anthonyjclarke/Solar-Lights-Lite/docs/drawings/breadboard-layout.png

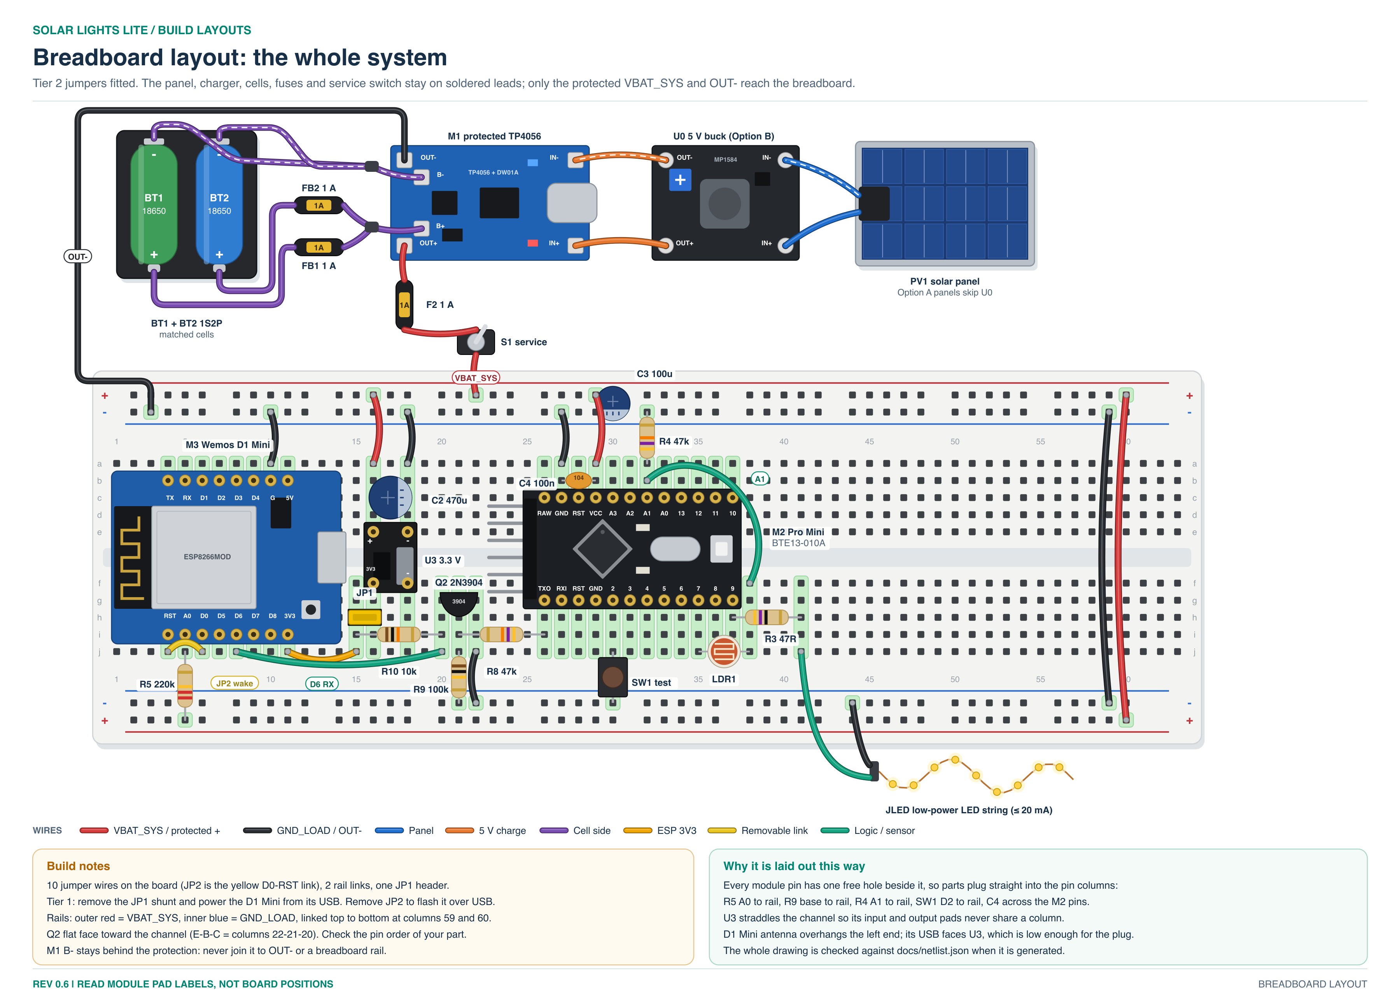
docs/drawings/breadboard-layout.png
