anthonyjclarke/Solar-Lights-Lite/docs/drawings/BTE13-010A-pin-map.png

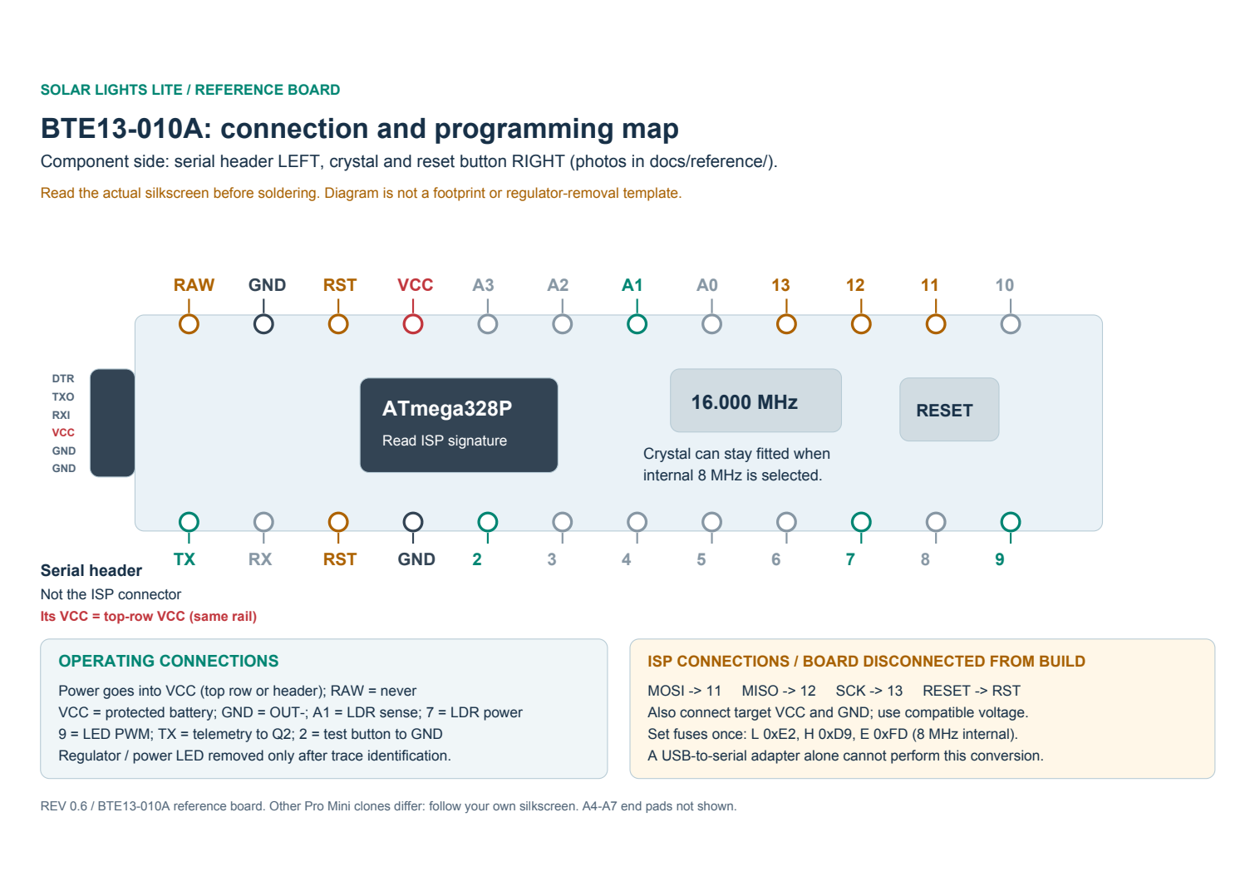
docs/drawings/BTE13-010A-pin-map.png
