anthonyjclarke/Solar-Lights-Lite/docs/drawings/controller-bench-sheet.png

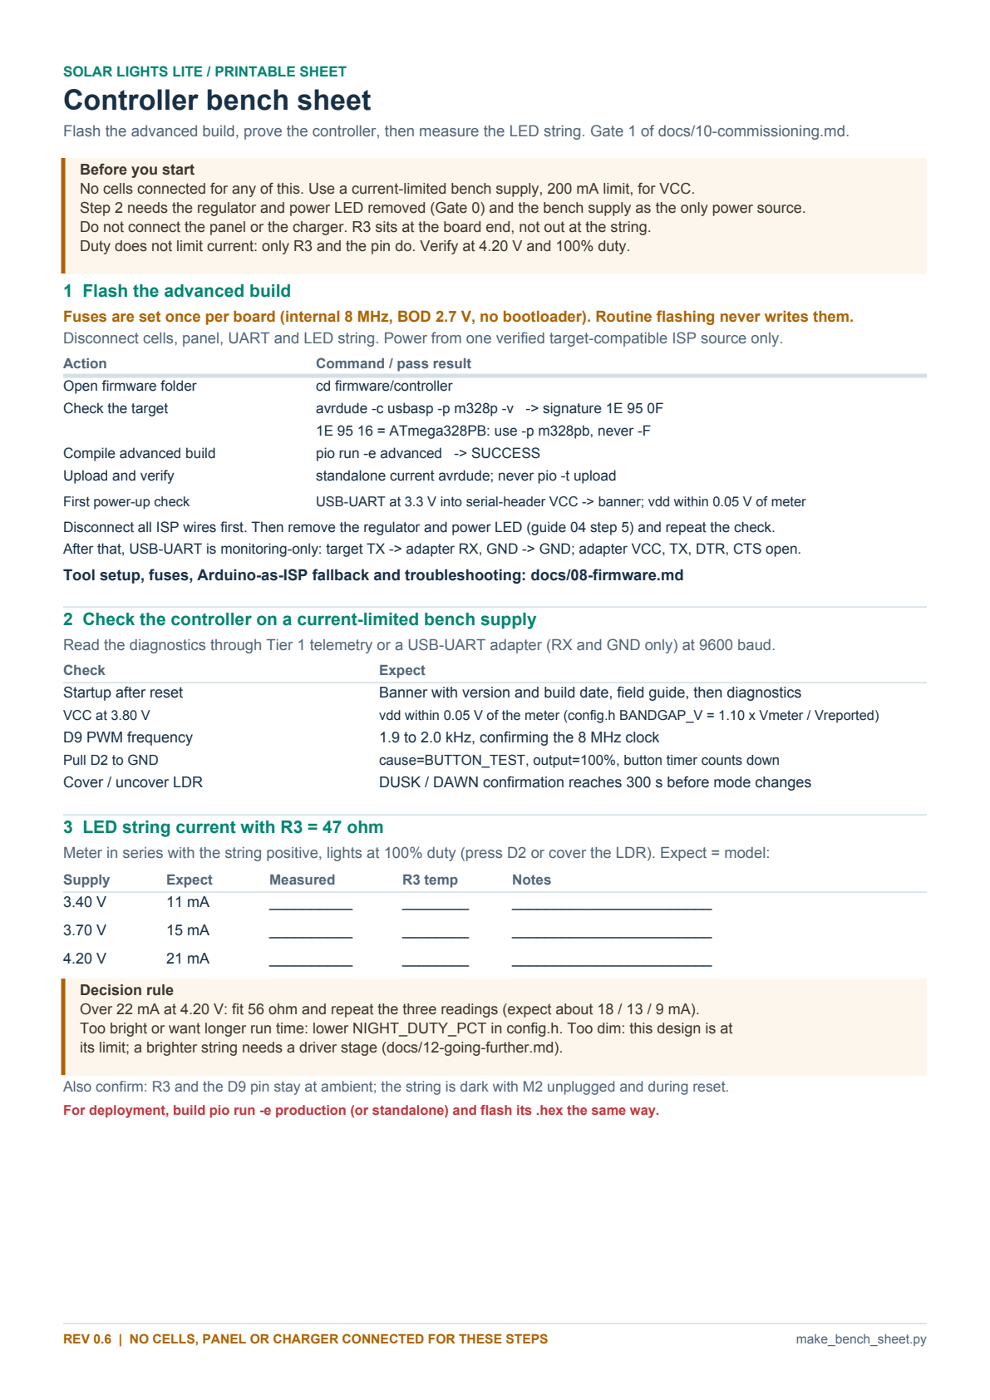
docs/drawings/controller-bench-sheet.png
