anthonyjclarke/Solar-Lights-Lite/docs/drawings/perfboard-layout.png

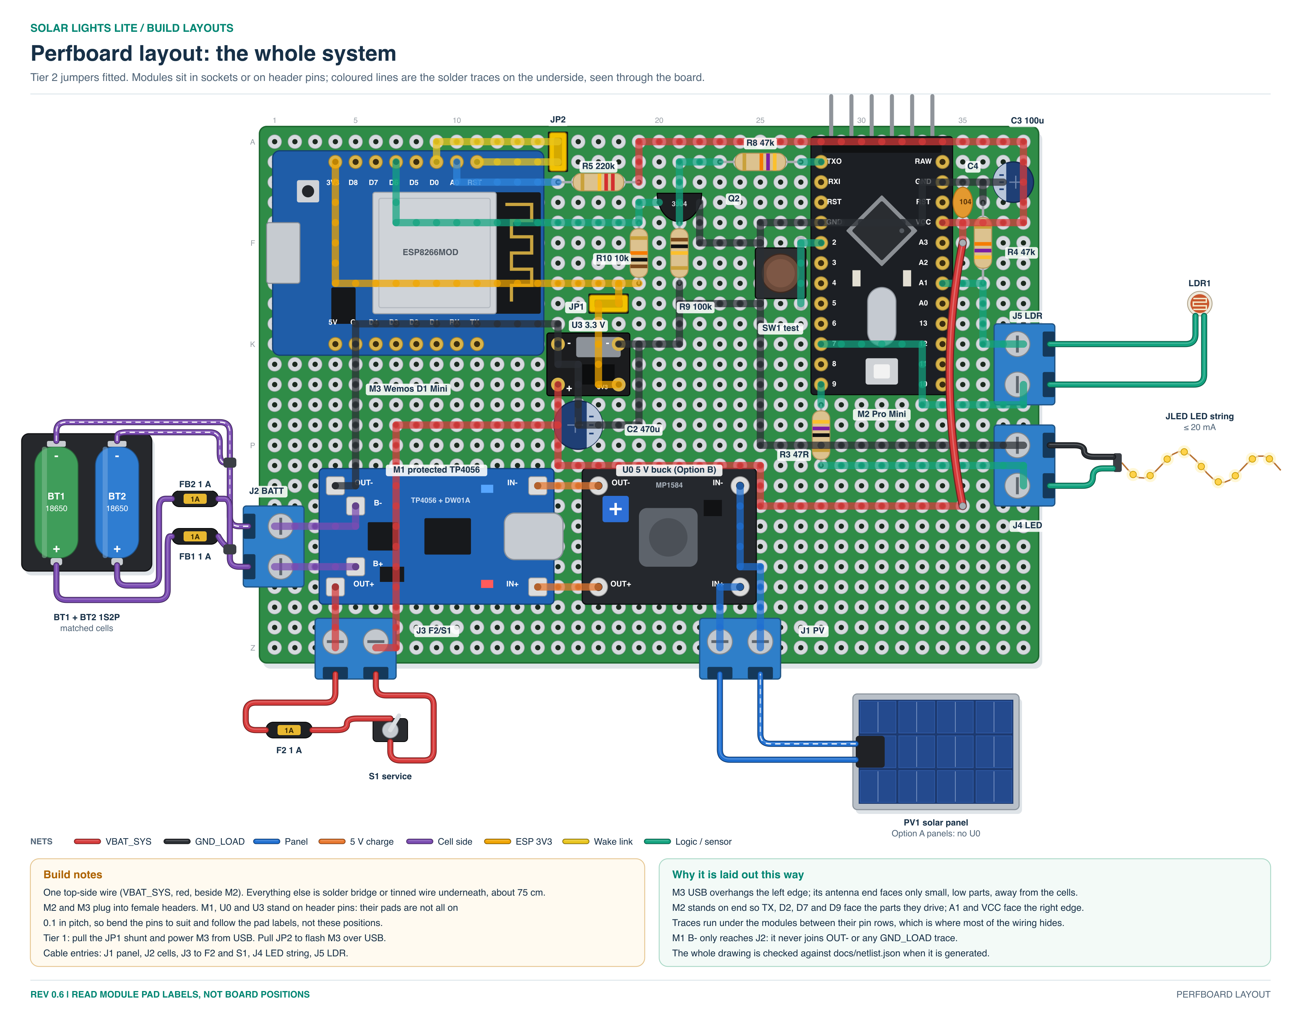
docs/drawings/perfboard-layout.png
