anthonyjclarke/Solar-Lights-Lite/docs/drawings/sheet-1.png

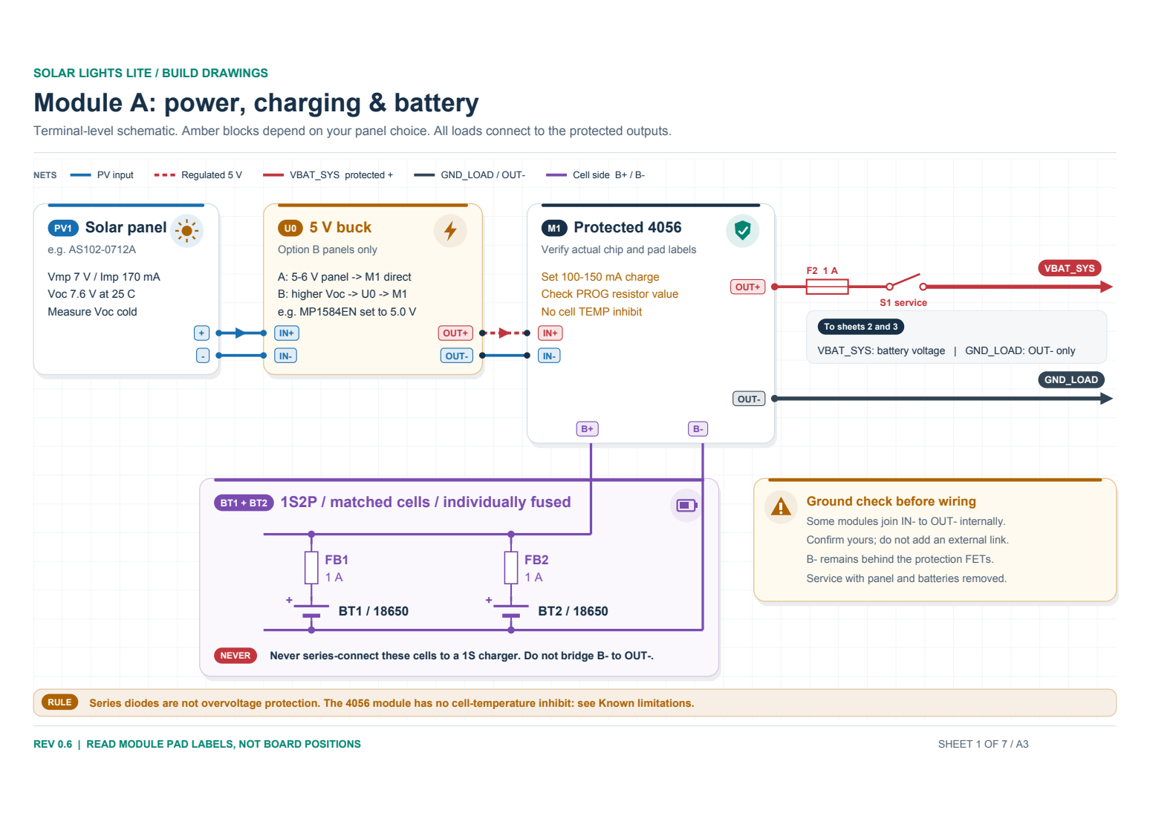
docs/drawings/sheet-1.png
