anthonyjclarke/Solar-Lights-Lite/docs/drawings/sheet-2.png

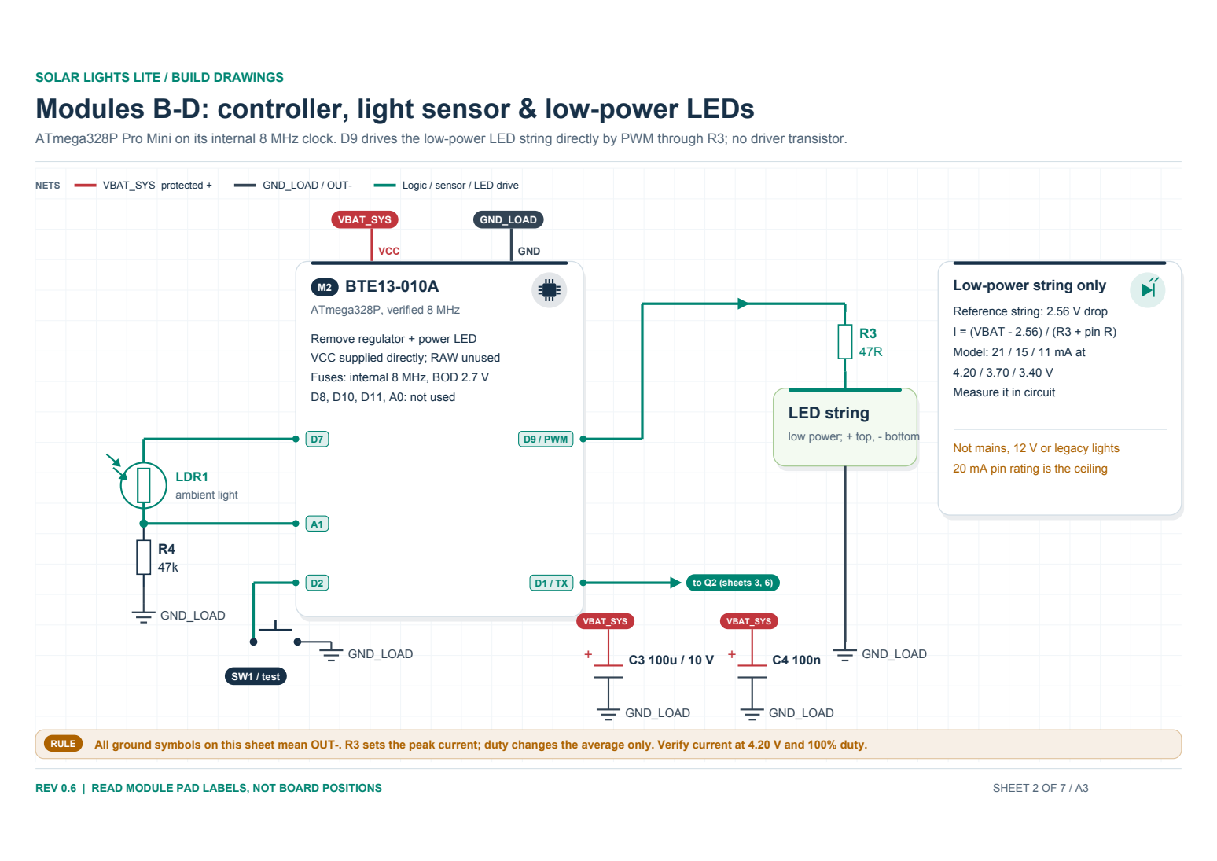
docs/drawings/sheet-2.png
