anthonyjclarke/Solar-Lights-Lite/docs/drawings/sheet-4.png

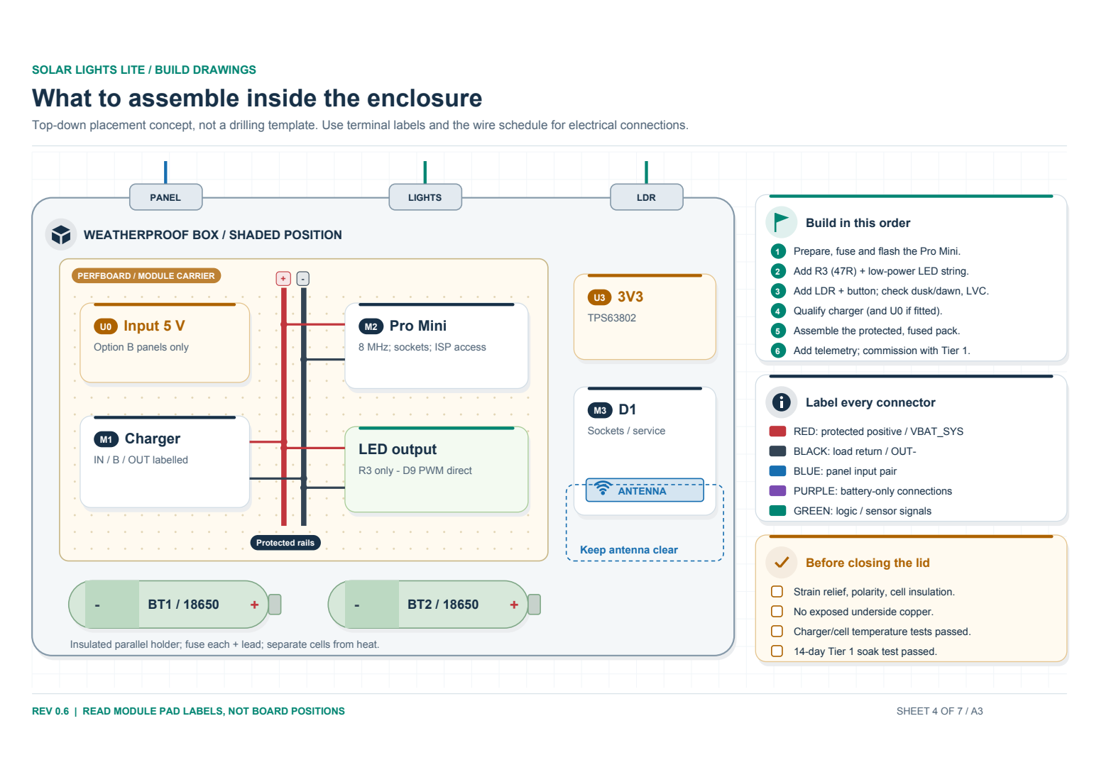
docs/drawings/sheet-4.png
