anthonyjclarke/Solar-Lights-Lite/docs/reference/BTE13-010A-front.jpeg

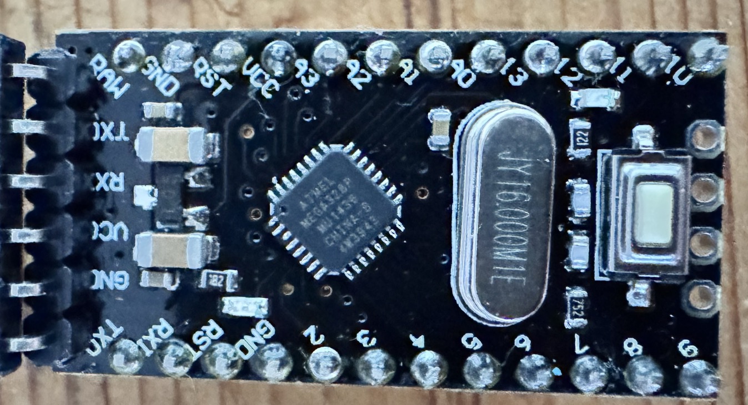
docs/reference/BTE13-010A-front.jpeg
