anthonyjclarke/Solar-Lights-Lite/docs/reference/charger-module-4056.jpg

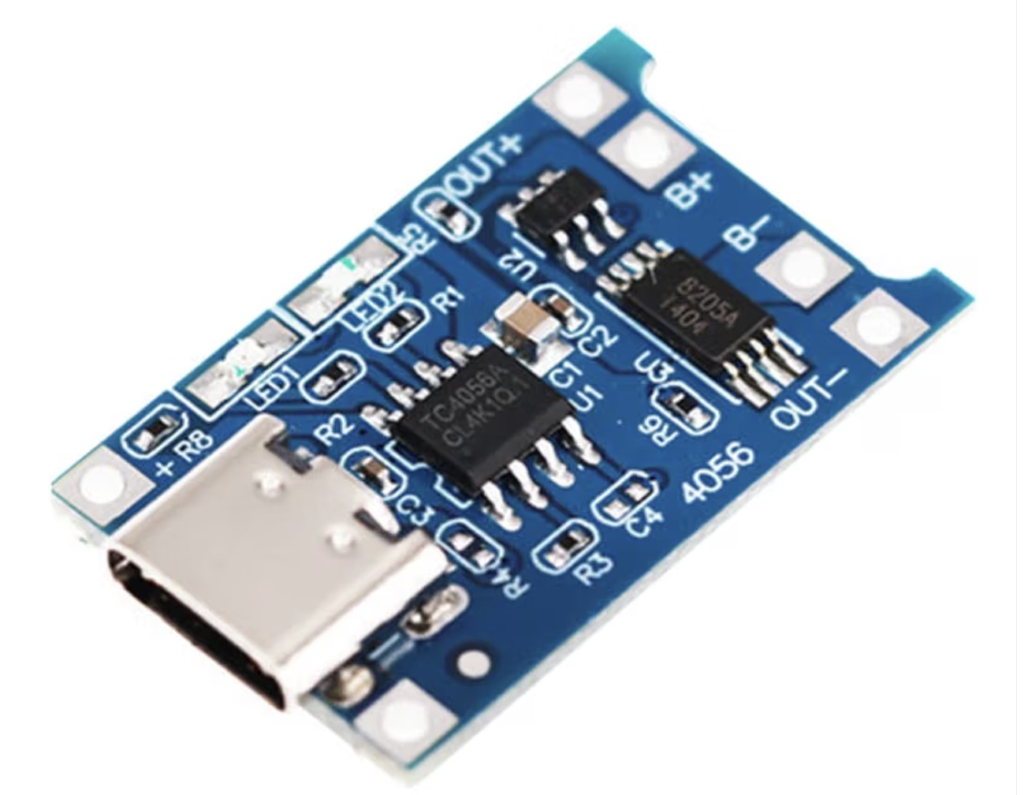
docs/reference/charger-module-4056.jpg
