anthonyjclarke/Solar-Lights-Lite/docs/reference/ProMini-328PB-front.jpeg

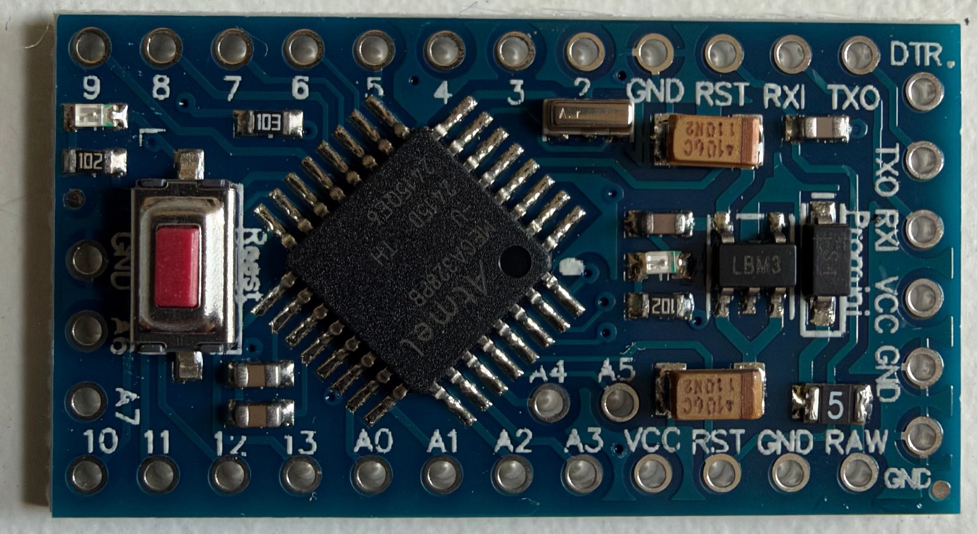
docs/reference/ProMini-328PB-front.jpeg
