anthonyjclarke/Solar-Lights-Lite/docs/reference/solar-panel-AS102-0712A.jpg

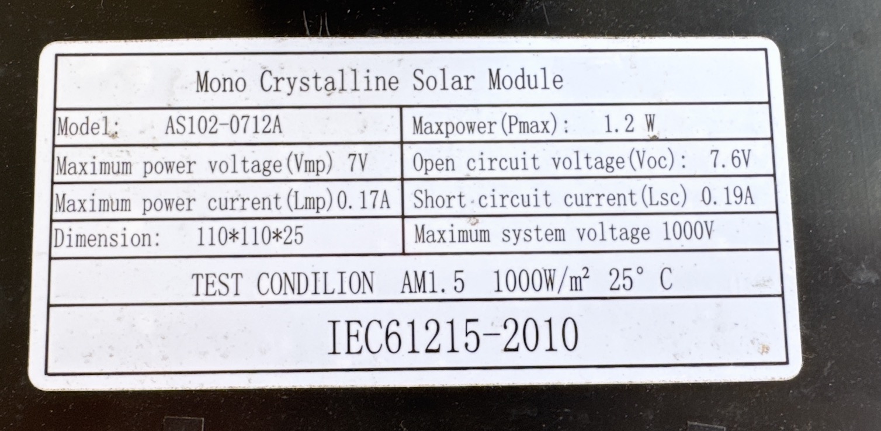
docs/reference/solar-panel-AS102-0712A.jpg
