anthonyjclarke/Solar-Lights-Lite/hardware/kicad/SolarLights_Lite.kicad_sch

## KiCad design hardware/kicad/SolarLights_Lite.kicad_sch (2026-09-30)

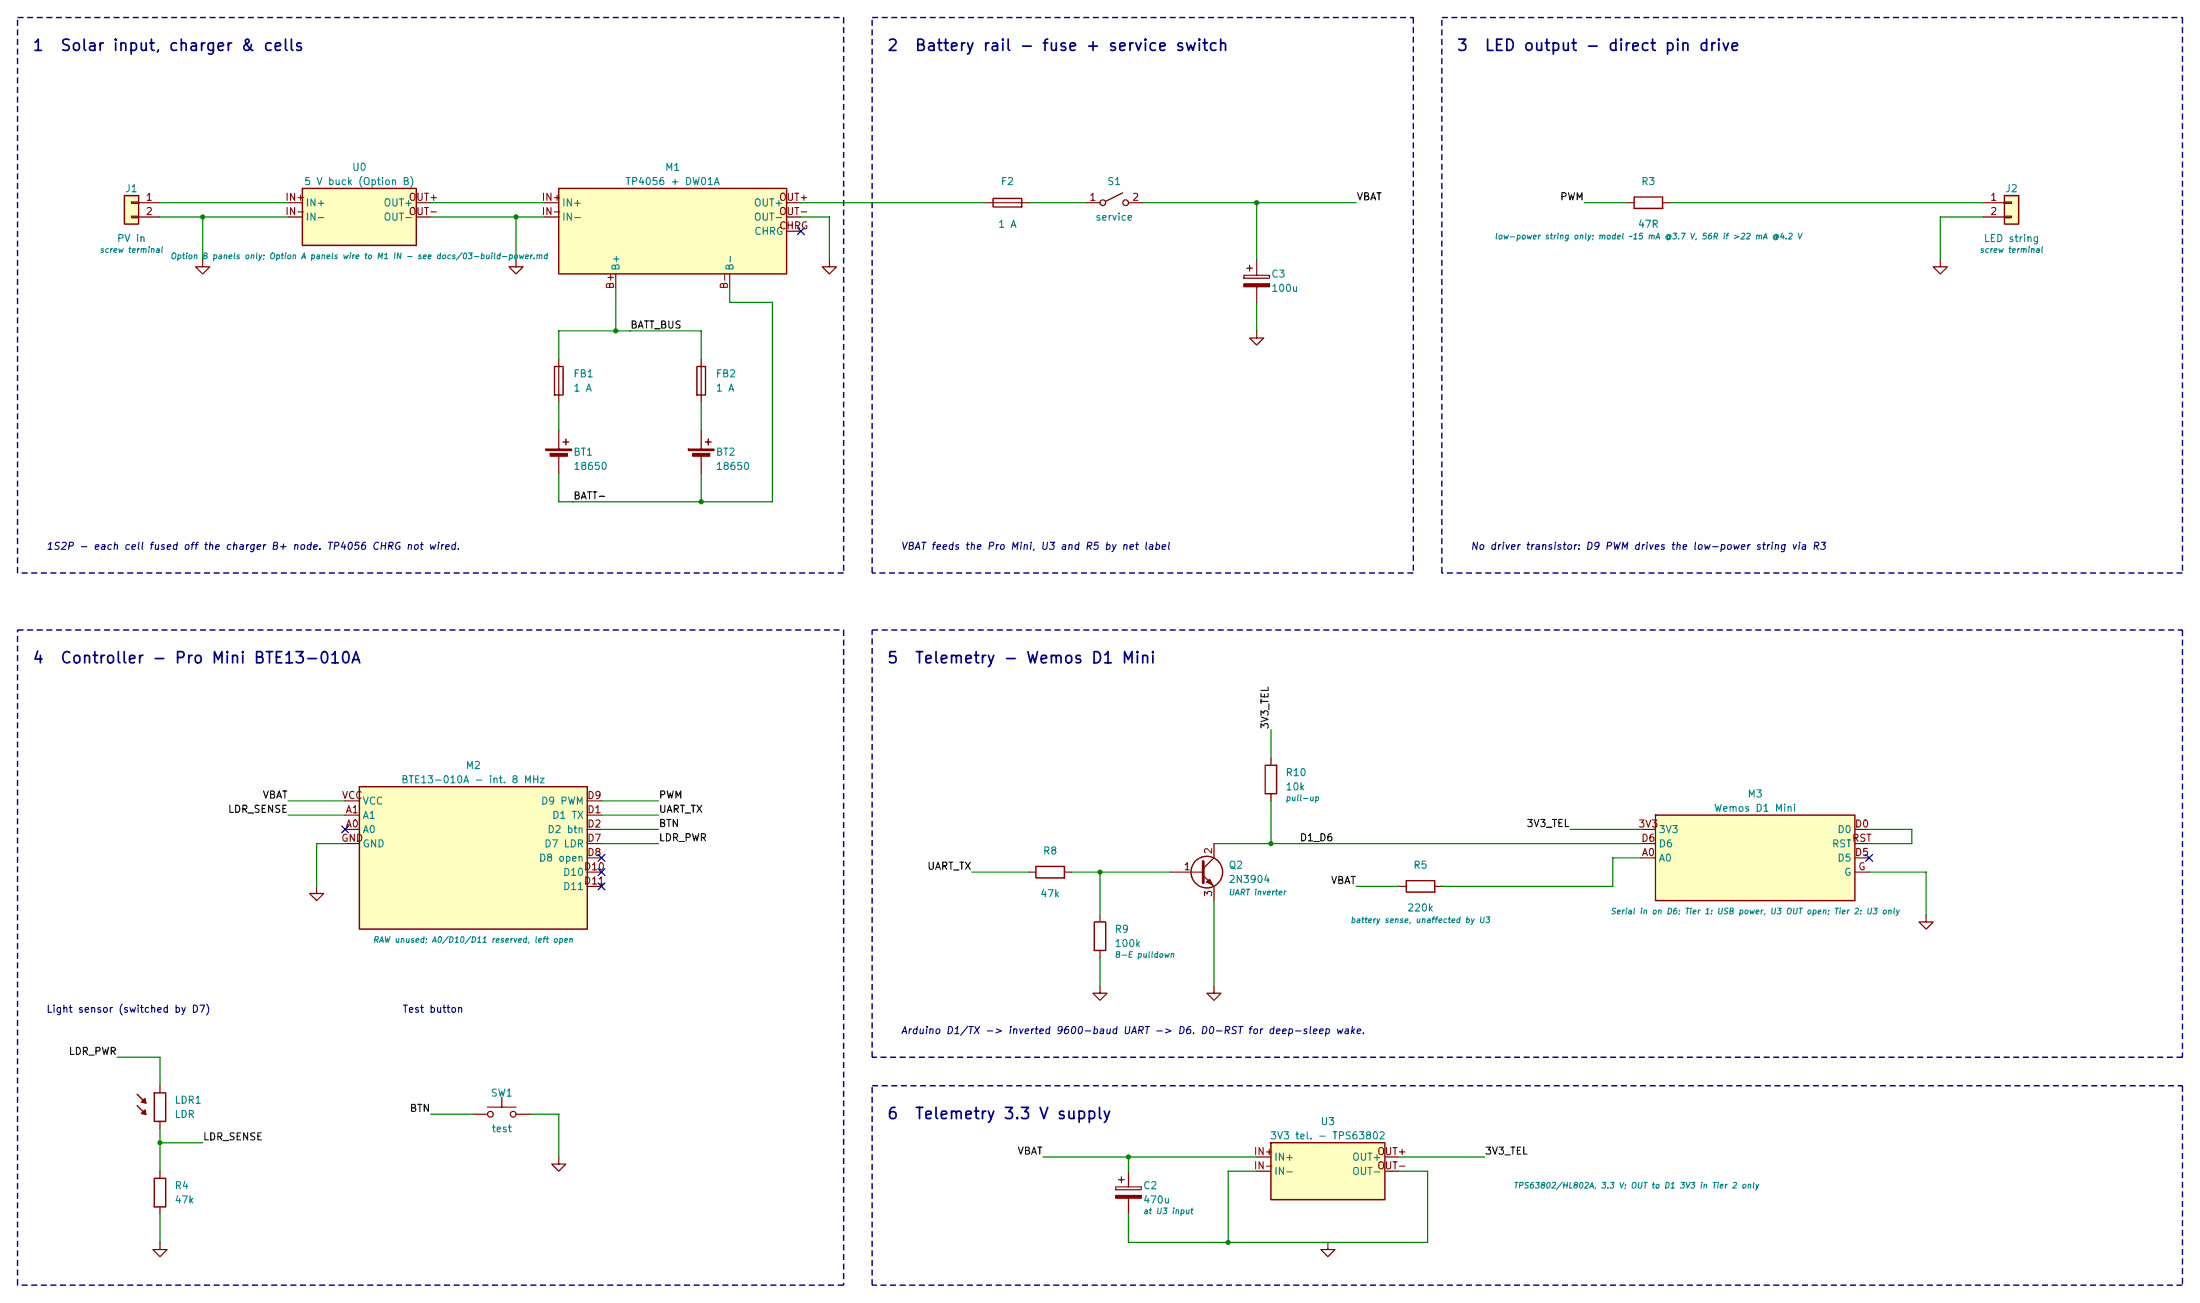
[picture p30: schematic SolarLights_Lite.kicad_sch]

Parts:
BT1, BT2: 18650
C2: 470u; CP_Radial_D6.3mm_P2.50mm
C3: 100u; CP_Radial_D6.3mm_P2.50mm
F2: 1 A
FB1, FB2: 1 A
J1: PV in
J2: LED string
LDR1: LDR
M1: TP4056 + DW01A
M2: BTE13-010A - int. 8 MHz
M3: Wemos D1 Mini
Q2: 2N3904
R3: 47R; R_Axial_DIN0207_L6.3mm_D2.5mm_P10.16mm_Horizontal
R4, R8: 47k; R_Axial_DIN0207_L6.3mm_D2.5mm_P10.16mm_Horizontal
R5: 220k; R_Axial_DIN0207_L6.3mm_D2.5mm_P10.16mm_Horizontal
R9: 100k; R_Axial_DIN0207_L6.3mm_D2.5mm_P10.16mm_Horizontal
R10: 10k; R_Axial_DIN0207_L6.3mm_D2.5mm_P10.16mm_Horizontal
S1: service
SW1: test
U0: 5 V buck (Option B)
U3: 3V3 tel. - TPS63802

Connections:
3V3_TEL: M3.3V3, R10.2, U3.OUT+
BATT-: BT1.2 (-), BT2.2 (-), M1.B- (B−)
BATT_BUS: FB1.1, FB2.1, M1.B+
BTN: M2.D2 (D2 btn), SW1.1
D1_D6: M3.D6, Q2.2 (C), R10.1
GND: C2.2, C3.2, J1.2, J2.2, M1.IN- (IN−), M1.OUT- (OUT−), M2.GND, M3.G, Q2.3 (E), R4.2, R9.2, SW1.2, U0.IN- (IN−), U0.OUT- (OUT−), U3.IN- (IN−), U3.OUT- (OUT−)
LDR_PWR: LDR1.1, M2.D7 (D7 LDR)
LDR_SENSE: LDR1.2, M2.A1, R4.1
unnamed: BT1.1 (+), FB1.2
unnamed: BT2.1 (+), FB2.2
unnamed: F2.1, M1.OUT+
unnamed: F2.2, S1.1 (A)
unnamed: J1.1, U0.IN+
unnamed: J2.1, R3.2
unnamed: M1.IN+, U0.OUT+
unnamed: M3.A0, R5.2
unnamed: M3.D0, M3.RST
unnamed: Q2.1 (B), R8.2, R9.1
PWM: M2.D9 (D9 PWM), R3.1
UART_TX: M2.D1 (D1 TX), R8.1
VBAT: C2.1, C3.1, M2.VCC, R5.1, S1.2 (B), U3.IN+

Notes on the sheet:
1 Solar input, charger & cells
2 Battery rail - fuse + service switch
3 LED output - direct pin drive
4 Controller - Pro Mini BTE13-010A
5 Telemetry - Wemos D1 Mini
6 Telemetry 3.3 V supply
1S2P - each cell fused off the charger B+ node. TP4056 CHRG not wired.
VBAT feeds the Pro Mini, U3 and R5 by net label
No driver transistor: D9 PWM drives the low-power string via R3
Light sensor (switched by D7)
Test button
Arduino D1/TX -> inverted 9600-baud UART -> D6. D0-RST for deep-sleep wake.
